nikolareljin/x240-kbd/docs/enclosure/index.md

---
title: Enclosure
nav_order: 40
has_children: true
---

# Enclosure

Two routes to a closed keyboard — 3D printed, or hand-made without a printer — plus how the
parts fit, what wears, and how to box the result.
